NJT999/Robotic-Arm-Project/STL Files/Screw_Gear.stl

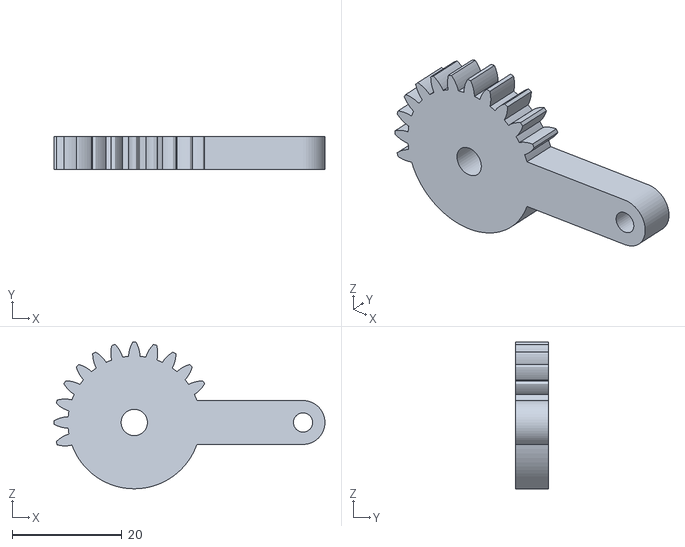
[picture p15: CAD file, 2026-08-14]
STL Files/Screw_Gear.stl
49.4 x 6.00 x 26.7
